sparkfun/Sparkpunk_Sequencer/sims/sparkpunk-sequencer.asc

C1: cap; 20µ
C2: cap; 1µf
C4: cap; 10µ
D1: LED
D2: LED
D3: LED
D4: LED
D5: LED
D6: schottky; 1N5817
D7: schottky; 1N5817
D8: schottky; 1N5817
D9: schottky; 1N5817
D10: LED
D11: schottky; 1N5817
D12: schottky; 1N5817
D13: diode
D14: diode
D15: LED
D16: LED
D17: schottky; 1N5817
D18: LED
D19: schottky; 1N5817
D20: schottky; 1N5817
D21: LED
D22: schottky; 1N5817
D23: schottky; 1N5817
D24: schottky; 1N5817
D25: schottky; 1N5817
D26: schottky; 1N5817
D27: schottky; 1N5817
D28: schottky; 1N5817
D29: schottky; 1N5817
D30: schottky; 1N5817
D31: schottky; 1N5817
D32: schottky; 1N5817
Q1: npn
Q2: npn
Q3: npn
Q4: npn
Q5: npn
Q6: npn; 2N3904
Q7: npn
Q8: npn
Q9: npn
Q10: npn
R1: res; 3k
R2: res; 10k
R3: res; 2k
R4: res; 9k
R5: res; 1k
R6: res; 100k
R7: res; 10k
R8: res; 2k
R9: res; 8k
R10: res; 2k
R11: res; 2k
R12: res; 4k
R13: res; 2k
R14: res; 9k
R15: res; 1k
R16: res; 6k
R17: res; 2k
R22: res; 2k
R23: res; 4k
R24: res; 6k
R25: res; 7k
R26: res; 3k
R27: res; 100k
R28: res; 10k
R29: res; 10k
R30: res; 10k
R32: res; 10k
R33: res; 22k
R35: res; 47k
R37: res; 33k
R38: res; 2k
R39: res; 8k
R40: res; 2k
R41: res; 47k
R42: res; 2k
R43: res; 7k
R44: res; 3k
R45: res; 100k
R46: res; 2k
R47: res; 3k
R48: res; 7k
R49: res; 100k
R50: res; 2k
R51: res; 5k
R52: res; 5k
R53: res; 10k
R54: res; 2k
R57: res; 2k
R58: res; 2k
R59: res; 100k
R60: res; 47k
R61: res; 22k
U1: CD4017B
U2: NE555
U3: UniversalOpamp2
U4: UniversalOpamp2
U5: CD4013B
U6: UniversalOpamp2
U7: UniversalOpamp2
U8: CD4013B
U10: UniversalOpamp2
U11: UniversalOpamp2
V1: voltage; 9
V2: voltage; PULSE(0 8 .5 .000001 .000001 .01 2)
Named nets: 0, VDD, step1, step2, step3, step4, POTSUM, gt, step5, step6, RST, last, PRECLK, step7, step8, step9, step10, CLK, gate2, cvout, rawcv, run, stop, clk
.inc CD4000_v.lib
.tran 0 30 0
R60: use 47K or 15K (15 = 47 || 22)
R54 is slide control, between 0 and 10K
R1 is tempo control, between 470 and 10,470
V2 simulates pulses coming from start/stop switch
