sparkfun/Sparkpunk_Sequencer/sims/seq2-invsum.asc

C1: cap; 100µ
C2: cap; 1µf
C3: cap; 10µ
D1: LED
D2: LED
D3: LED
D4: LED
D5: LED
D6: schottky; 1N5817
D7: schottky; 1N5817
D8: schottky; 1N5817
D9: schottky; 1N5817
D10: LED
D11: schottky; 1N5817
D12: schottky; 1N5817
D13: diode
D14: diode
D15: LED
D16: LED
D17: schottky; 1N5817
D18: LED
D19: schottky; 1N5817
D20: schottky; 1N5817
D21: LED
D22: schottky; 1N5817
D23: schottky; 1N5817
D24: schottky; 1N5817
D25: schottky; 1N5817
D26: schottky; 1N5817
D27: schottky; 1N5817
D28: schottky; 1N5817
D29: schottky; 1N5817
D30: schottky; 1N5817
D31: schottky; 1N5817
D32: schottky; 1N5817
Q1: npn
Q2: npn
Q3: npn
Q4: npn
Q5: npn
Q6: npn; 2N3904
Q7: npn
Q8: npn
Q9: npn
Q10: npn
R1: res; 1k
R2: res; 10k
R3: res; 2k
R4: res; 5k
R5: res; 5k
R6: res; 100k
R7: res; 5k
R8: res; 2k
R9: res; 2k
R10: res; 8k
R11: res; 2k
R12: res; 2k
R13: res; 2k
R14: res; 8k
R15: res; 2k
R16: res; 8k
R17: res; 2k
R18: res; 100k
R19: res; 10k
R20: res; 10k
R21: res; 5k
R22: res; 2k
R23: res; 1
R24: res; 10k
R25: res; 8k
R26: res; 2k
R27: res; 100k
R28: res; 10K
R29: res; 10K
R30: res; 10K
R31: res; 10K
R32: res; 10k
R33: res; 10K
R34: res; 6k8
R35: res; 10K
R36: res; 5k
R38: res; 2k
R39: res; 8k
R40: res; 2k
R42: res; 2k
R43: res; 8k
R44: res; 2k
R46: res; 2k
R47: res; 8k
R48: res; 2k
R50: res; 2k
R51: res; 8k
R52: res; 2k
R55: res; 33k
R56: res; 47k
U1: CD4017B
U2: NE555
U3: UniversalOpamp2
U4: UniversalOpamp2
U5: CD4013B
U8: UniversalOpamp2
U9: UniversalOpamp2
V1: voltage; 5
V2: voltage; PULSE(0 8 .5 .000001 .000001 .01 2)
V3: voltage; PULSE(1 2 0 10)
V4: voltage; 2.5
Named nets: 0, VDD, step1, step2, step3, step4, POTSUM, gt, VREF, step5, step6, last, RST, CLK, VREF2, step7, step8, step9, step10, gate2, cvout
.inc CD4000_v.lib
.tran 0 10 0
47k = legato, 377k = stacc
Transpose input, ground if unused
100k = legato, 33k = stacc??
